utsxumiao/AffoFly/Content/Images/AffoFly_MultiWii_Board_Layout_01.jpg

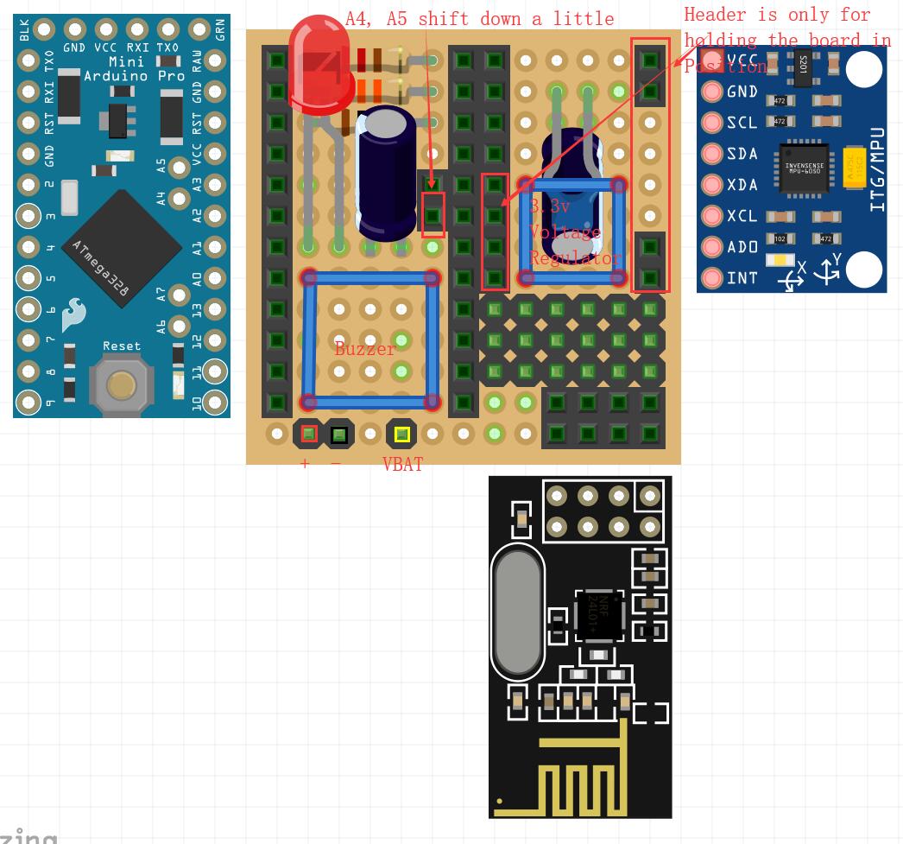
Content/Images/AffoFly_MultiWii_Board_Layout_01.jpg
