utsxumiao/AffoFly/Content/Images/AffoFly_RX_PPM_1ms.jpg

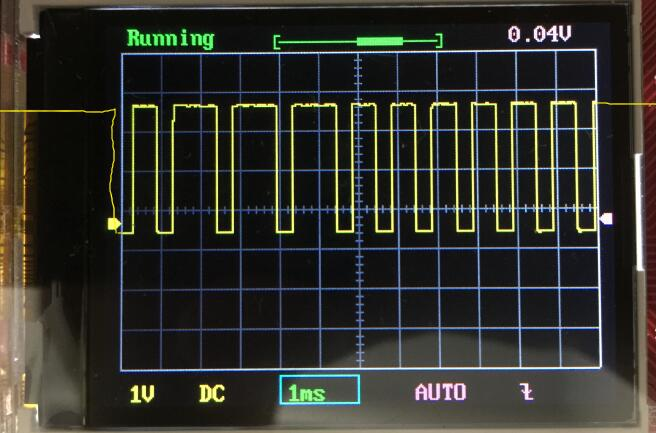
Content/Images/AffoFly_RX_PPM_1ms.jpg
