utsxumiao/AffoFly/Content/Images/AffoFly_RX_PPM_5ms.jpg

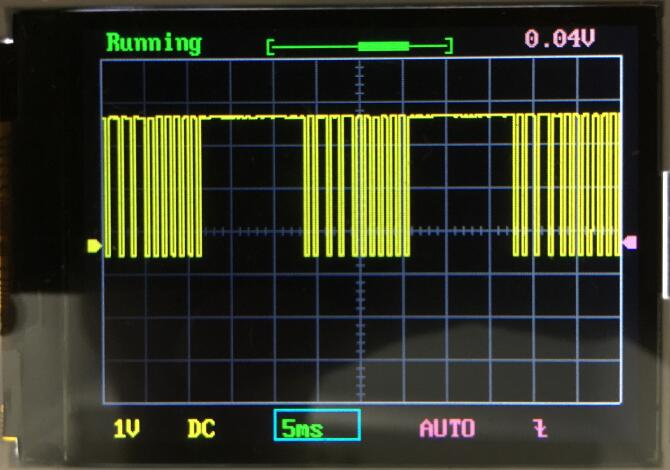
Content/Images/AffoFly_RX_PPM_5ms.jpg
